Cylindric3D/uv-box/Box/bottom-back.SLDPRT

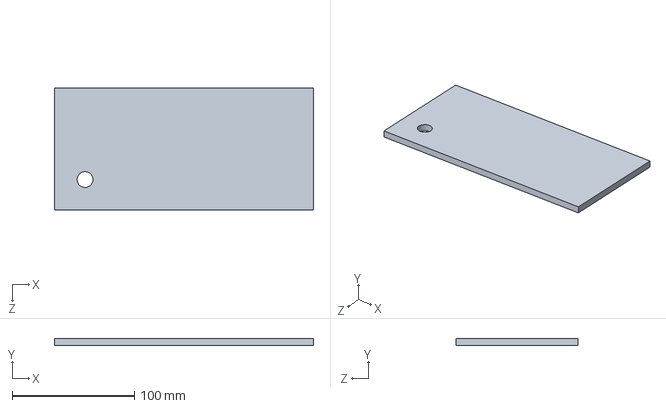
[picture p17: CAD file, 2014-12-01]
Box/bottom-back.SLDPRT
212.0 x 6.00 x 100.0 mm
