Cylindric3D/uv-box/Box/top-front.SLDPRT

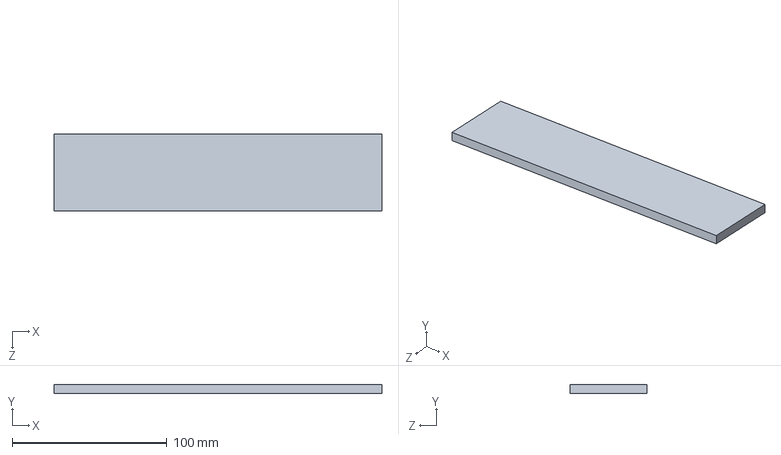
[picture p18: CAD file, 2014-12-01]
Box/top-front.SLDPRT
212.0 x 6.00 x 50.0 mm
