Cylindric3D/uv-box/Box/bottom-frontinsert.SLDPRT

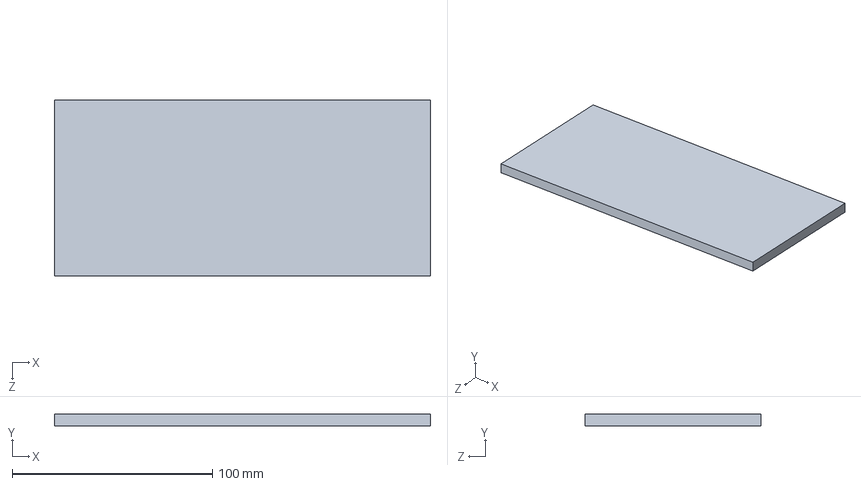
[picture p19: CAD file, 2014-12-01]
Box/bottom-frontinsert.SLDPRT
188.0 x 6.00 x 88.0 mm
