Cylindric3D/uv-box/Box/top-side.SLDPRT

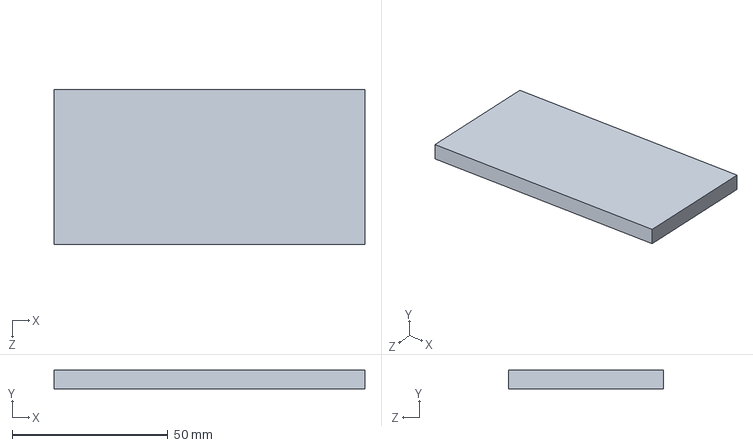
[picture p20: CAD file, 2014-12-01]
Box/top-side.SLDPRT
100.0 x 6.00 x 50.0 mm
