Cylindric3D/uv-box/Box/bottom-side.SLDPRT

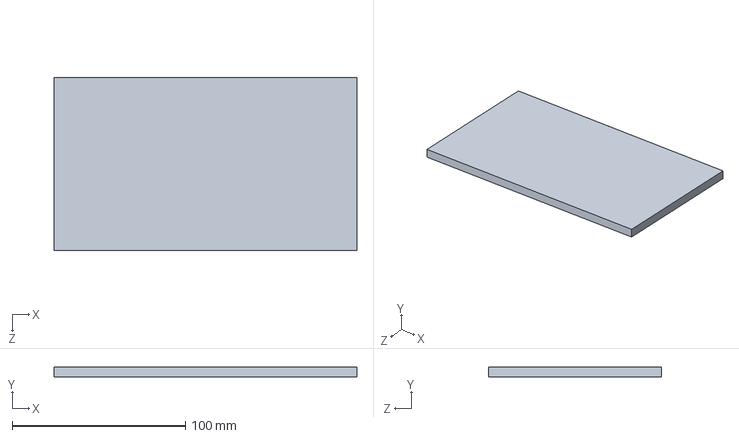
[picture p21: CAD file, 2014-12-01]
Box/bottom-side.SLDPRT
175.0 x 6.00 x 100.0 mm
