Cylindric3D/uv-box/Box/bottom-base.SLDPRT

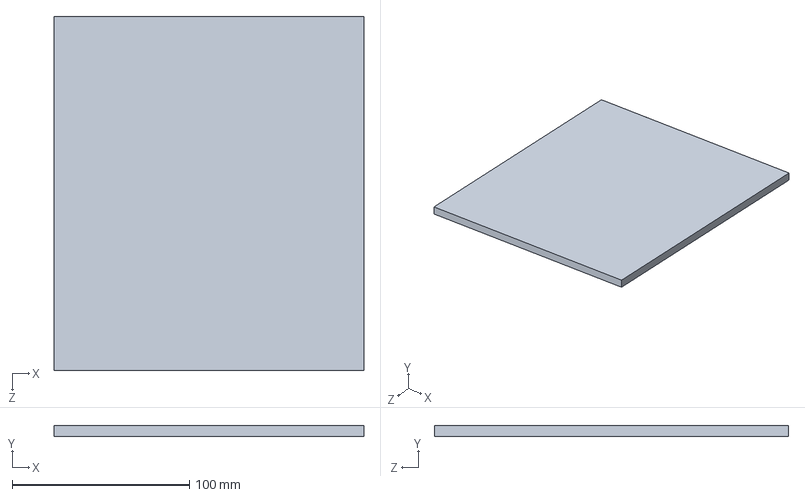
[picture p22: CAD file, 2014-12-01]
Box/bottom-base.SLDPRT
175.0 x 6.00 x 200.0 mm
