Cylindric3D/uv-box/Box/top-top.SLDPRT

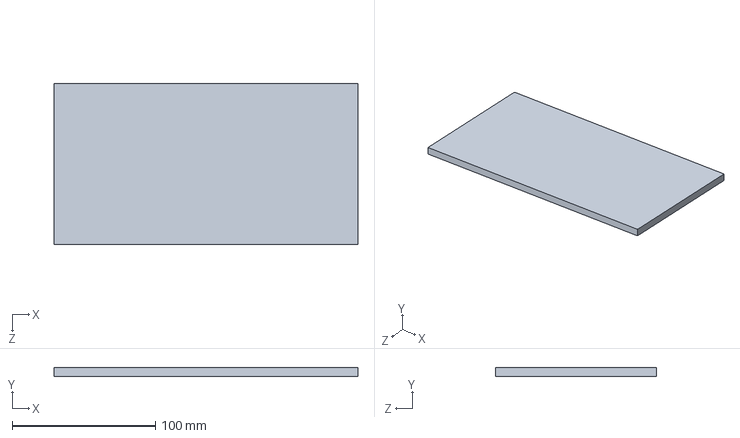
[picture p23: CAD file, 2014-12-01]
Box/top-top.SLDPRT
212.0 x 6.00 x 112.0 mm
