Cylindric3D/uv-box/Box/bottom-step.SLDPRT

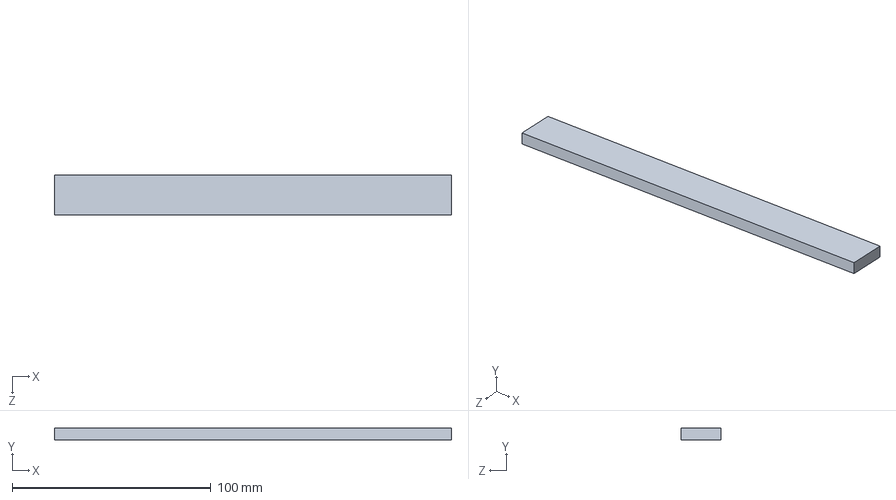
[picture p24: CAD file, 2014-12-01]
Box/bottom-step.SLDPRT
200.0 x 6.00 x 20.0 mm
